Vonger/V7B_WS2812B/ch32v003/Peripheral/src/ch32v00x_it.c

void NMI_Handler(void) __attribute__((interrupt("WCH-Interrupt-fast")));
void HardFault_Handler(void) __attribute__((interrupt("WCH-Interrupt-fast")));

void NMI_Handler(void)
{
}

void HardFault_Handler(void)
{
  while (1)
  {
  }
}
